SteveRMann/netMonitor/netMonitor/netMonitor.ino

#define SKETCH "netMonitor"
#define VERSION "7.10"           // Four characters
#define hostPrefix "NETMON"      // Six characters max

/*
   This program pings essential IP addresses, and if no response is received, it lights a red LED.
   If all pings are good, it lights a green LED

   PCB built on a Wemos D1 Mini (ESP8266)

   Version 3.0 9/4/2019
     Working with three-color LEDs
   Version 3.1 10/3/2019
     Removed local router from the ping list, added plex server.
     (If the router is offline, no other pings would work anyway).
     Added Eagle folder to the git
   Version 4.0 2/17/2020
     Added OTA.
   Version 5.0 8/25/2020
     Added mqtt to publish ping errors to be logged.
   Version 5.1 3/10/2021
     Publish the failing IP.
   Version 5.2 3/12/2021
     Added four new and removed two problematic external IPs
   Version 5.3 3/16/2021
     Check for MQTT connection with each ping. Log all fails.
   Version 6.0 3/24/21
     Made the hostName dynamic, prefix+last 3 bytes of the MAC
     Use hostName for MQTT connect.
   Version 6.1 9/11/2021
     Fixed a comma error in iplist.h
   Version 6.2 3/06/2022
     Added Red, Green, Blue, Yellow to the startup sequence
     Changed WiFi.ino to WiFiMulti.ino
   Version 6.2.4 3/12/2022
     Removed sirius.com from the external list.
   Version 6.2.5 11/5/2022
     Removed outlook.com from the external list.
   Version 7.00 12/17/22
     Removed MQTT
   Version 7.1  11/8/2023
     Added  WiFi.disconnect(true); to Setup_Wifi()
     Removed WiFiMulti()

*/



//-------------------------
#include <ESP8266Ping.h>        // Includes ESP8266WiFi.h
#include <Wire.h>               // Wire.h is the library for communicating with I2C devices
#include <ArduinoOTA.h>
#include <Kaywinnet.h>          // WiFi credentials


// setup_wifi vars
char macBuffer[24];       // Holds the last three digits of the MAC, in hex.
char hostNamePrefix[] = hostPrefix;
char hostName[24];        // Holds hostNamePrefix + the last three bytes of the MAC address.


#include <dlay.h>
dlay  aTimer;                   // Allocate a global timer.


#define DEBUG true              // Set to true for debug output, false for no debug ouput
#define Serial if(DEBUG)Serial
#define DBUG                    // If defined, show more debug statements

#define blueLedPin 14               // Pin D5 on NodeMcu or Wemos D1 Mini (Blue LED)

int myBits = 0;
int ledNum  = 0;

//-------------------------

// IP's to ping.
#include "ipList.h"
const int webIpCount = (sizeof(ipx) / sizeof(ipx[0])) - 3;
unsigned int pingDelay = 10000;       //Ping all IP's then wait (in ms) before pinging again.



//-------------------------
//for LED status
#include <Ticker.h>
Ticker blueTicker;                //Ticker object for the WiFi Connecting LED
Ticker greenTicker;               //Ticker object for the Ping Activity LED



// ****************************  Function to blink LED on pin D5 ****************************
void blueTick() {
  //toggle state
  int state = digitalRead(blueLedPin);            // get the current state of GPIO14 pin
  digitalWrite(blueLedPin, !state);               // set pin to the opposite state
}



// ****************************  Function to blink LED[i] ****************************
void greenTick() {
  // Toggle the LED
  bitWrite(myBits, ledNum , !bitRead(myBits, ledNum ));
  wSend(myBits);
  delay(40);
}


// **************************** Function to send a byte to the LED array. ****************************
void wSend (byte wData) {
  //Send the data to the MCP23008
  Wire.beginTransmission(0x20);   //Start talking to the slave device.
  Wire.write(0x09);               //Select the GPIO pins.
  Wire.write(wData);              //Writing a 1 to the pin turns it on, while writing a 0 turns it off.
  Wire.endTransmission();         //ends communication with the device
}




// **************************** Function to print an 8-bit binary number. ****************************
// Usage: printBinaryByte(0x97);
// Prints: "10010111"
void printBinaryByte(byte value) {
  for (byte mask = 0x80; mask; mask >>= 1)
  {
    Serial.print((mask & value) ? '1' : '0');
  }
}


// **************************** Function to checksum a string. ****************************
byte stringChecksum(char *s)
{
  byte c = 0;
  while (*s != '\0')
    c ^= *s++;
  return c;
}

// ********************** Function to display a string for debugging. **********************
void dbugs(const char *s, const char *v) {
  //Show a string variable. Enter with the string description and the string.
  //Example dbugs("My String= ",myString);
  Serial.print(s);
  Serial.print (F("\""));
  Serial.print(v);
  Serial.println(F("\""));
}
