SteveRMann/netMonitor/netMonitor2/hosts.h

IPAddress ipAddressArray[] = {
  IPAddress(192, 168, 1, 64),   // Gallifrey (Plex)
  IPAddress(192, 168, 1, 124),  // Broker
  IPAddress(192, 168, 1, 57),   // Home Assistant
  IPAddress(192, 168, 1, 111)   // Zeus
};

const char* hosts[] = {
  "amazon.com",
  "yahoo.com",
  "google.com"
};
