SteveRMann/netMonitor/netMonitor2/WiFi.ino

// setup_wifi
// ============================= Connect the ESP to the router =============================
// Connect to WiFi network so we can reach the MQTT broker and publish messages to topics.

/*
  Make sure you include at the start of the sketch:
  #define SKETCH "netMonitor"

  #include "ESP8266WiFi.h"        // Not needed if also using the Arduino OTA Library...
  #include <Kaywinnet.h>          // WiFi credentials

  char macBuffer[24];             // Holds the last three digits of the MAC, in hex.
  char hostName[24];              // Holds nodeName + the last three bytes of the MAC address.

  const char WIFISSID[] = NSSID;      //Select the network credentials
  const char WIFIPASS[] = NPASSWORD;
*/

void setup_wifi() {
#ifndef Kaywinnet
#include <Kaywinnet.h>
#endif
  byte mac[6];                    // The MAC address of your Wifi

  Serial.println(F("\n"));
  Serial.print(F("Connecting to "));
  Serial.println(WIFISSID);
  Serial.print(F("Password: "));
  Serial.println(WIFIPASS);

  // Disconnect from the current WiFi network and reset WiFi configuration
  WiFi.disconnect(true);

  /* Explicitly set the ESP8266 to be a WiFi-client, otherwise, it by default,
     would try to act as both a client and an access-point and could cause
     network-issues with your other WiFi-devices on your WiFi-network. */
  WiFi.mode(WIFI_STA);
  WiFi.begin(WIFISSID, WIFIPASS);
  while (WiFi.status() != WL_CONNECTED) {
    delay(500);
    Serial.print(WiFi.status());
    if (WiFi.status() == 4) {
      ESP.restart();
    }
  }
  Serial.println(F("\nWiFi connected, "));
  Serial.print(F("MAC Address: "));
  Serial.println(WiFi.macAddress());
  Serial.print(F("IP address: "));
  Serial.println(WiFi.localIP());


  // Get the last three numbers of the mac address.
  // "4C:11:AE:0D:83:86" becomes "0D8386" in macBuffer.
  WiFi.macAddress(mac);
  snprintf(macBuffer, sizeof(macBuffer), "%02X%02X%02X", mac[3], mac[4], mac[5]);

  // Build hostName from prefix + last three bytes of the MAC address.
  strcpy(hostName, "netmon");
  strcat(hostName, "-");
  strcat(hostName, macBuffer);
  WiFi.hostname(hostName);
  Serial.print(F("hostName= "));
  Serial.println(hostName);
}
