SteveRMann/netMonitor/netMonitor/iplist.h

const char* ipx[] = {
  "192.168.1.64",       // Plex Server
  "192.168.1.124",      // MQTT Broker
  "192.168.1.57",       // Home Assistant on NUC
  // Web IPs, ping one at random per loop
  "173.223.17.209",     // akami.com
  "205.251.242.103",    // amazon.com
  "130.211.34.48",      // cbs.com
  "23.46.189.181",      // CVS.com
  "63.119.85.89",		// deltadental.com
  "31.13.71.36",        // facebook.com
  "140.82.113.3",       // github.com
  "172.217.165.133",	// gmail.com
  "104.18.22.165",      // Hillsdale.edu
  "104.25.24.31",       // home-assistant.io
  "204.52.196.176",		// mypanera.com
  "23.39.32.154",       // nbc.com
  "192.0.66.176",       // newscorp.com
  "104.21.86.26",       // nodered.org
  "45.60.12.113",		// Safeway.com
  "23.192.111.135",     // sears.com
  "140.82.112.3",       // github.com
  "104.244.42.1",       // twitter.com
  "192.16.31.89",	    // verizon.net
  "23.1.99.98",         // Walgreens.com
  "208.80.154.224",     // wikipedia.org
  "204.141.42.155"      // Zoho.com
};
